Koumbaya/Aegis/pictures/20210312_100416.jpg

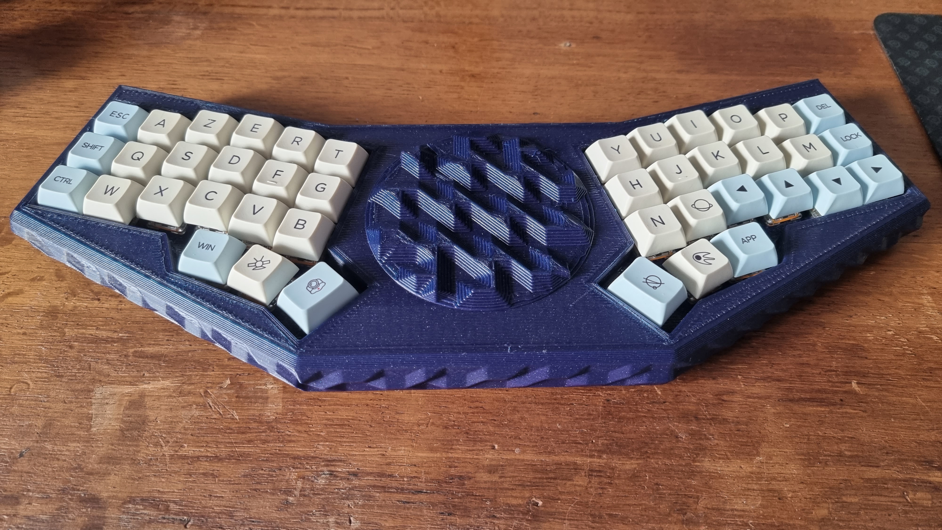
pictures/20210312_100416.jpg
