Koumbaya/Aegis/pictures/20210312_100429.jpg

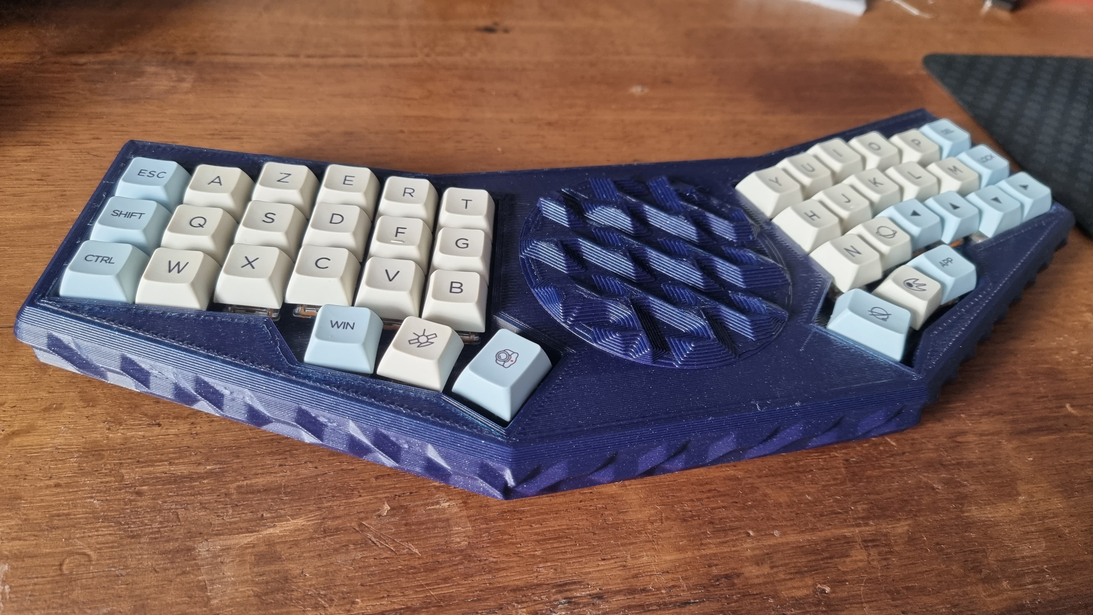
pictures/20210312_100429.jpg
