Koumbaya/Aegis/pictures/20210312_100509.jpg

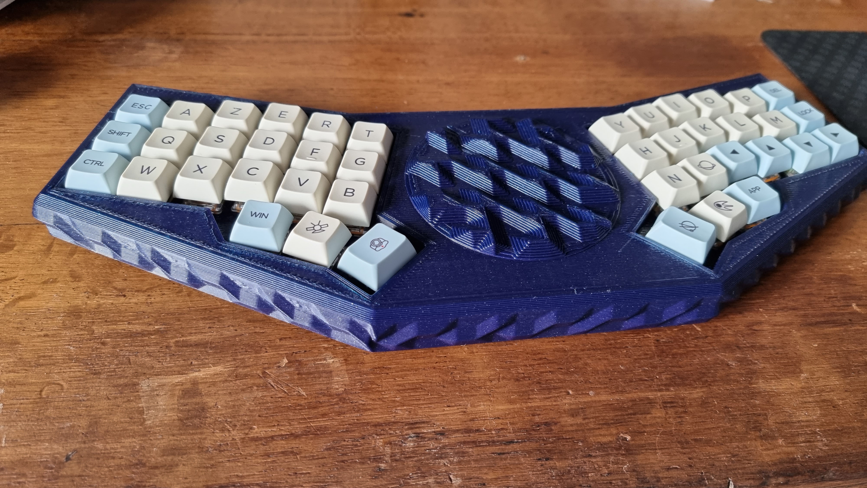
pictures/20210312_100509.jpg
