Koumbaya/Aegis/pictures/20210312_100549.jpg

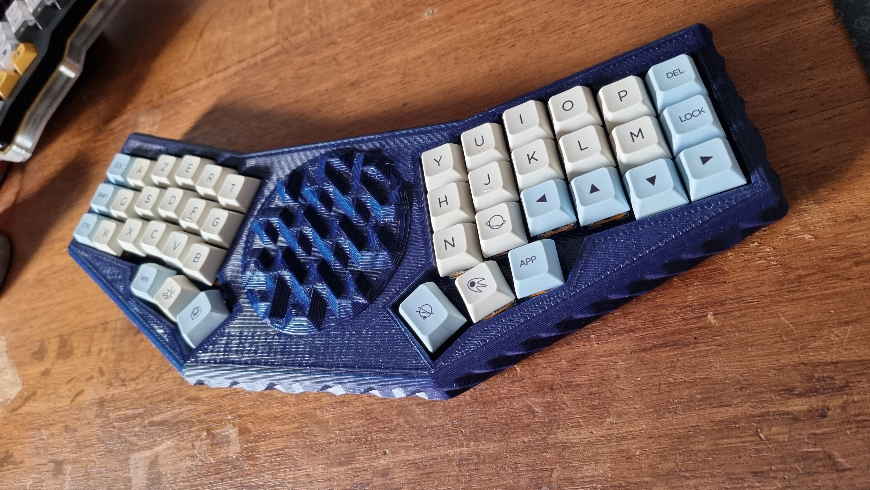
pictures/20210312_100549.jpg
