Koumbaya/Aegis/case_aegis_version/Aegis_bottom.SLDPRT

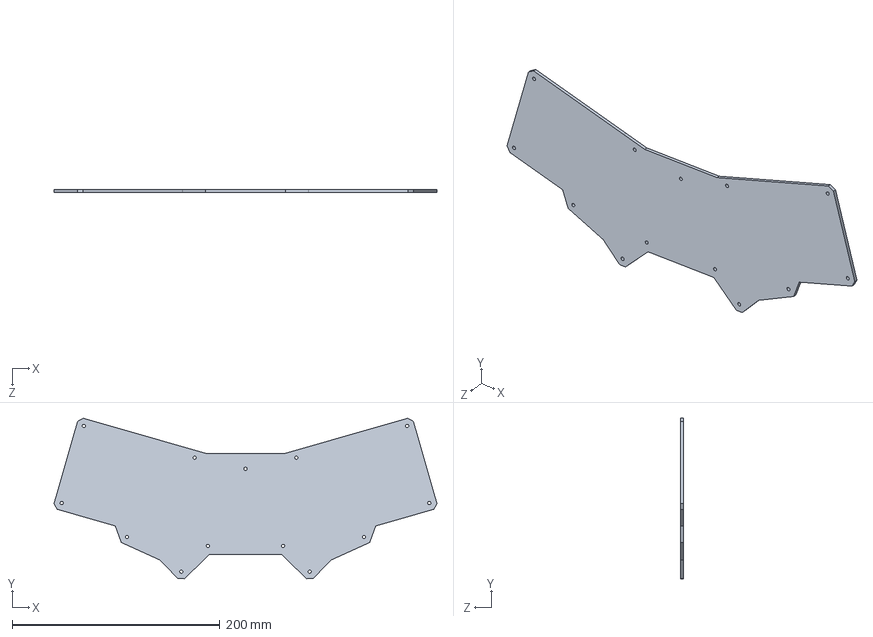
[picture p25: CAD file, 2020-11-01]
case_aegis_version/Aegis_bottom.SLDPRT
369.1 x 154.7 x 3.00 mm
