Koumbaya/Aegis/case_aegis_version/cutouts/Aegis_bottom.DXF

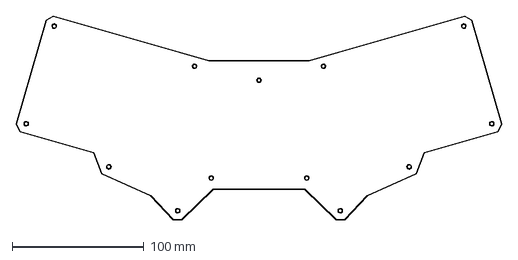
[picture p26: CAD file, 2020-10-25]
case_aegis_version/cutouts/Aegis_bottom.DXF
369.1 x 154.7 mm
