Koumbaya/Aegis/case_crkbd_version/cutouts/Aegis_top2.DXF

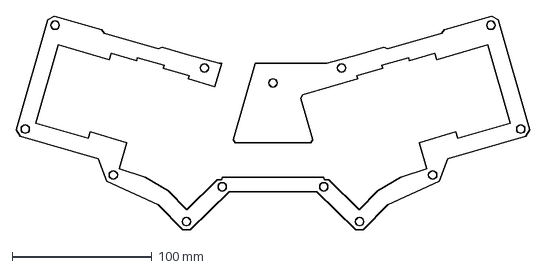
[picture p27: CAD file, 2020-10-31]
case_crkbd_version/cutouts/Aegis_top2.DXF
366.9 x 152.6 mm
