Koumbaya/Aegis/case_aegis_version/Aegis_top1.SLDPRT

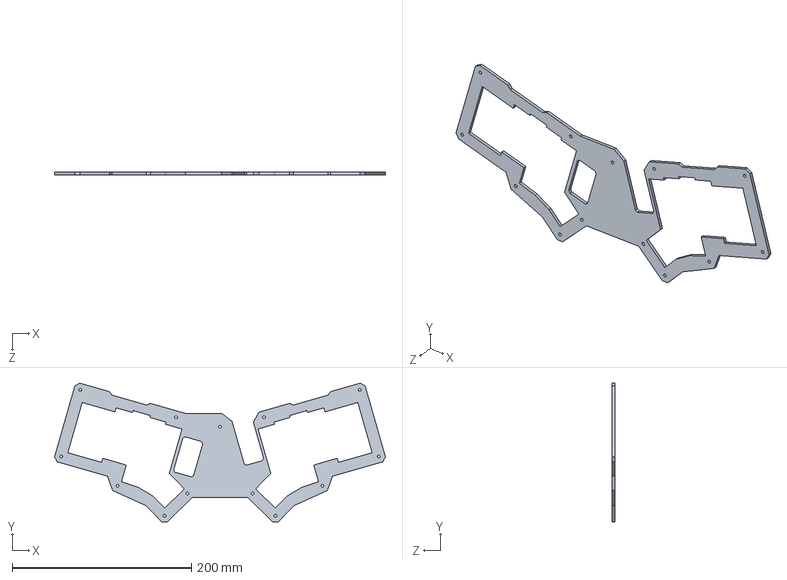
[picture p28: CAD file, 2020-11-01]
case_aegis_version/Aegis_top1.SLDPRT
369.1 x 154.7 x 3.00 mm
