Koumbaya/Aegis/case_aegis_version/cutouts/Aegis_middle.DXF

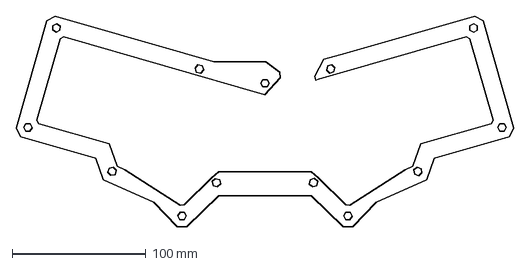
[picture p29: CAD file, 2020-10-25]
case_aegis_version/cutouts/Aegis_middle.DXF
371.9 x 157.4 mm
