Koumbaya/Aegis/case_crkbd_version/Aegis_top2.SLDPRT

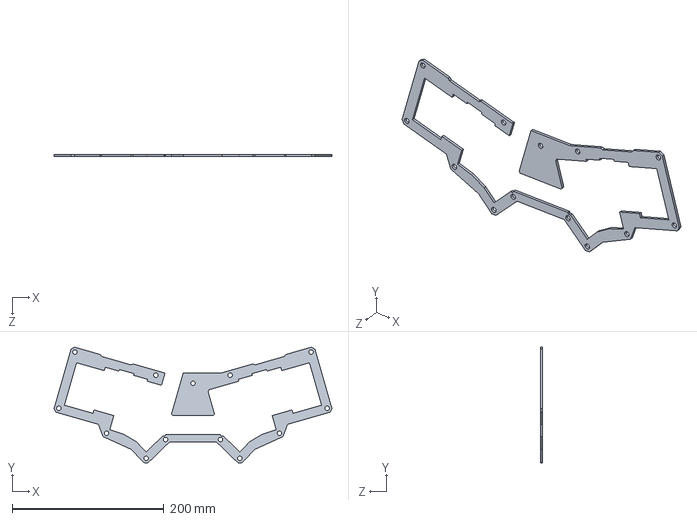
[picture p30: CAD file, 2020-10-31]
case_crkbd_version/Aegis_top2.SLDPRT
366.9 x 152.6 x 3.00 mm
