Koumbaya/Aegis/case_crkbd_version/cutouts/Aegis_top1.DXF

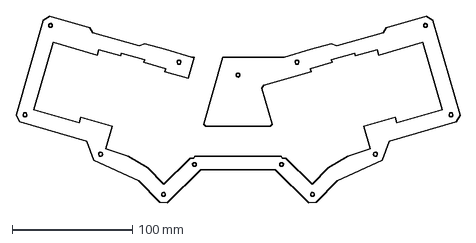
[picture p31: CAD file, 2020-10-31]
case_crkbd_version/cutouts/Aegis_top1.DXF
369.1 x 154.7 mm
