Koumbaya/Aegis/case_aegis_version/Aegis_switch_plate_nologo.SLDPRT

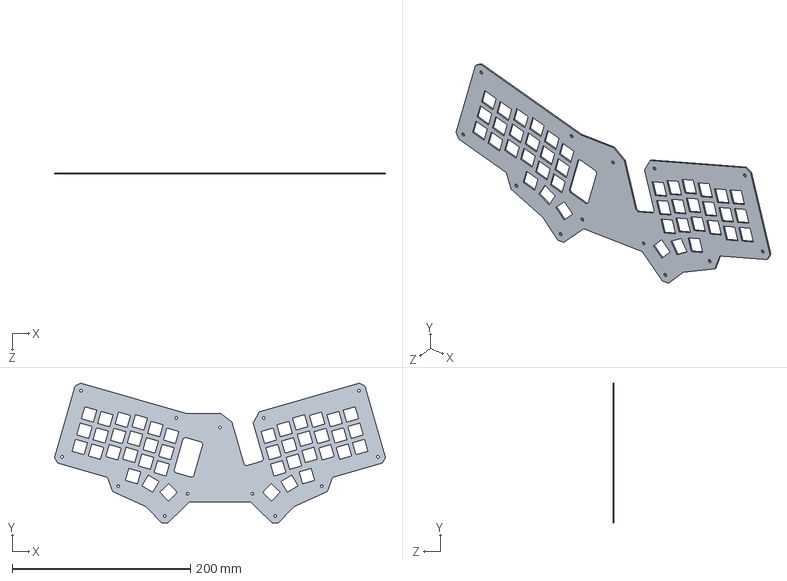
[picture p32: CAD file, 2020-11-01]
case_aegis_version/Aegis_switch_plate_nologo.SLDPRT
371.2 x 156.7 x 1.50 mm
