Koumbaya/Aegis/case_aegis_version/cutouts/Aegis_switch_plate.DXF

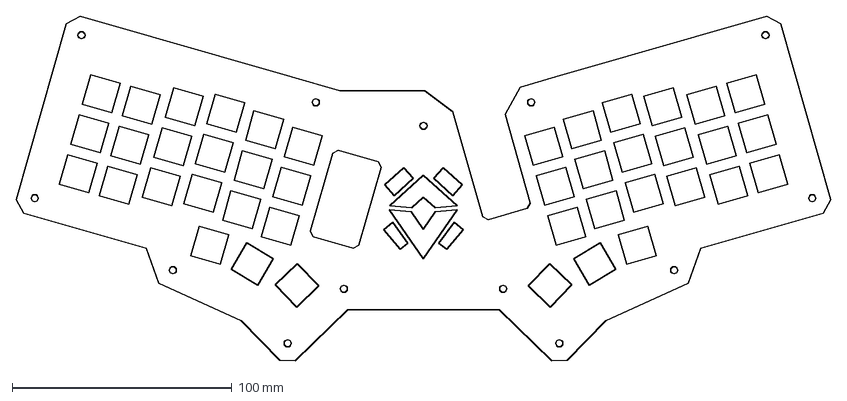
[picture p33: CAD file, 2020-10-25]
case_aegis_version/cutouts/Aegis_switch_plate.DXF
371.2 x 156.7 mm
