Koumbaya/Aegis/case_crkbd_version/Aegis_middle.SLDPRT

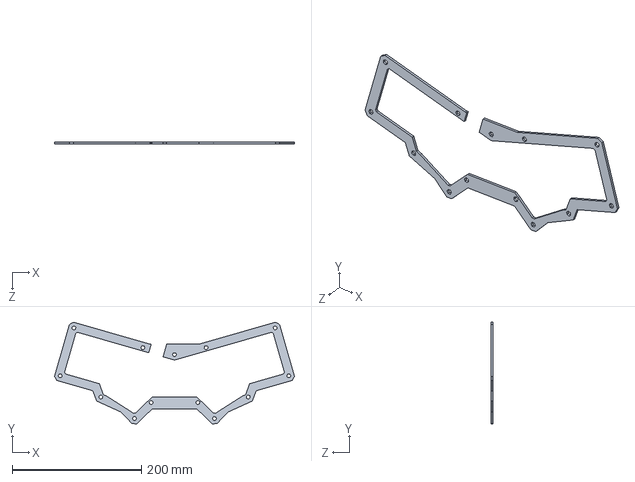
[picture p34: CAD file, 2020-10-31]
case_crkbd_version/Aegis_middle.SLDPRT
371.9 x 157.4 x 3.00 mm
