Koumbaya/Aegis/case_aegis_version/Aegis_top3.SLDPRT

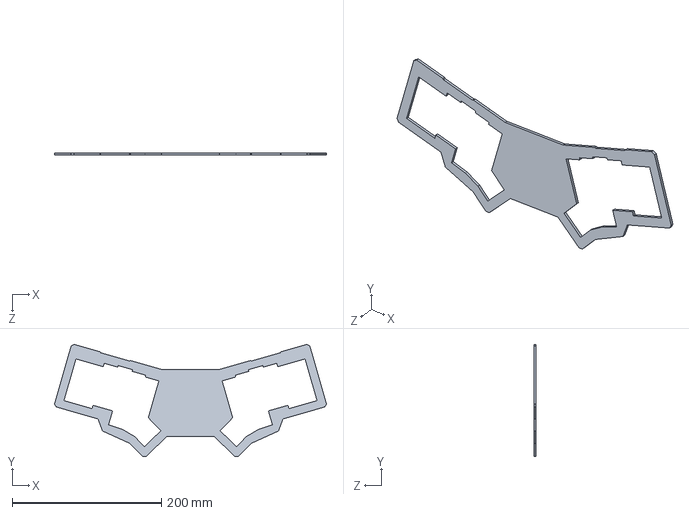
[picture p35: CAD file, 2020-11-01]
case_aegis_version/Aegis_top3.SLDPRT
364.8 x 150.5 x 3.00 mm
