Koumbaya/Aegis/case_aegis_version/cutouts/Aegis_top1.DXF

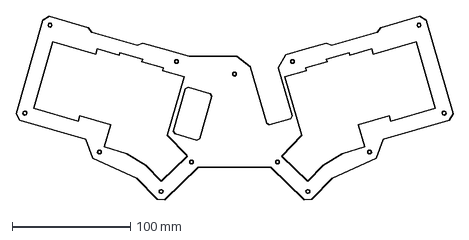
[picture p36: CAD file, 2020-10-25]
case_aegis_version/cutouts/Aegis_top1.DXF
369.1 x 154.7 mm
