Koumbaya/Aegis/case_crkbd_version/cutouts/Aegis_top3.DXF

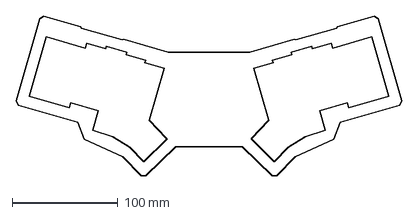
[picture p37: CAD file, 2020-10-25]
case_crkbd_version/cutouts/Aegis_top3.DXF
364.8 x 150.5 mm
