Koumbaya/Aegis/case_crkbd_version/PCB.SLDPRT

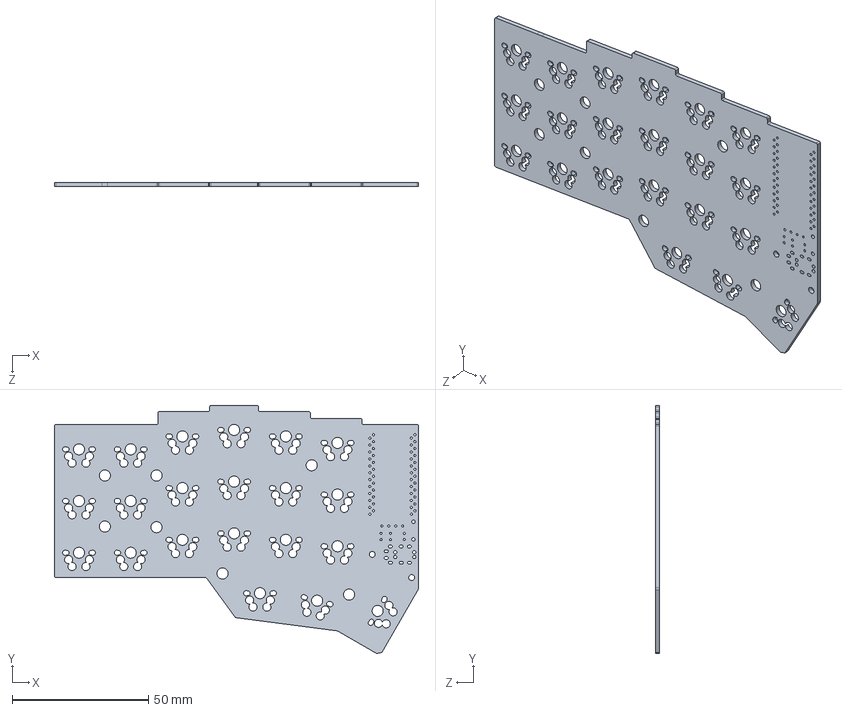
[picture p38: CAD file, 2020-10-31]
case_crkbd_version/PCB.SLDPRT
133.8 x 91.2 x 1.60 mm
