Koumbaya/Aegis/case_aegis_version/Aegis_top2.SLDPRT

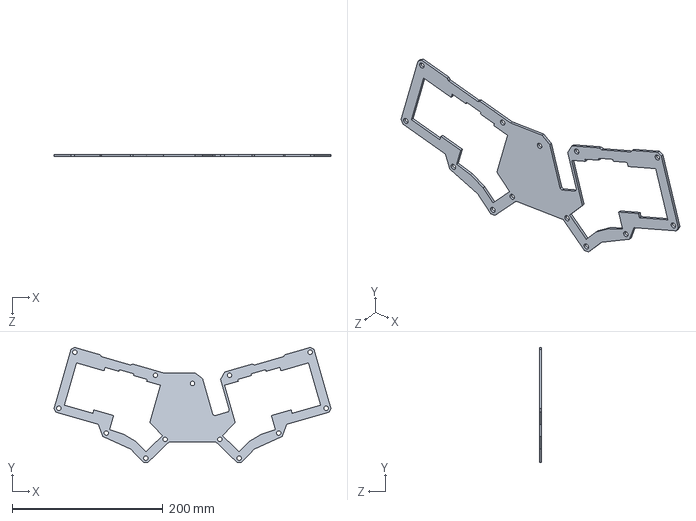
[picture p39: CAD file, 2020-11-01]
case_aegis_version/Aegis_top2.SLDPRT
366.9 x 152.6 x 3.00 mm
