Koumbaya/Aegis/case_aegis_version/cutouts/pcb_model.DXF

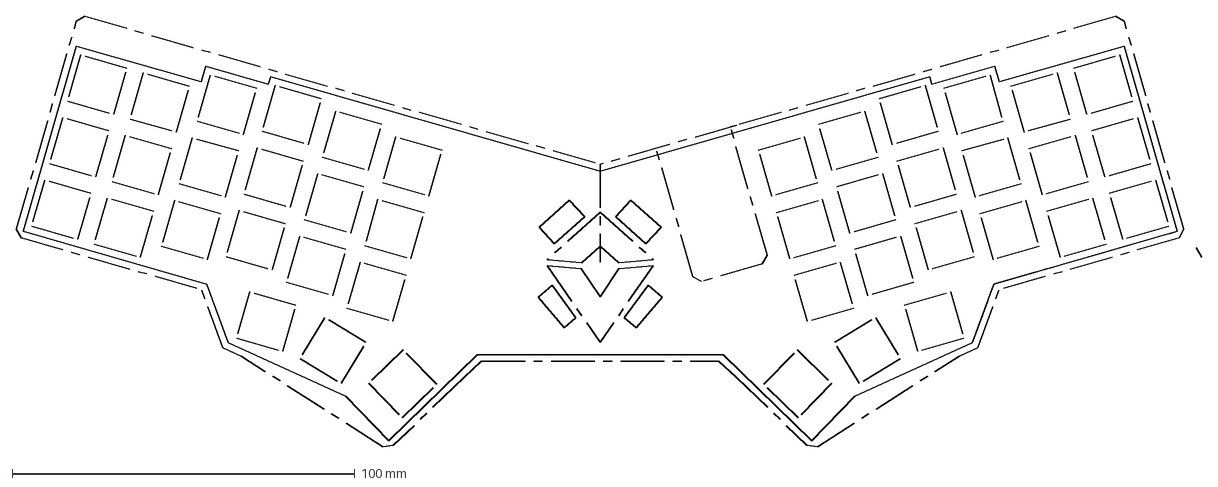
[picture p40: CAD file, 2020-10-24]
case_aegis_version/cutouts/pcb_model.DXF
345.8 x 125.5 mm
