Koumbaya/Aegis/case_aegis_version/Aegis_middle.SLDPRT

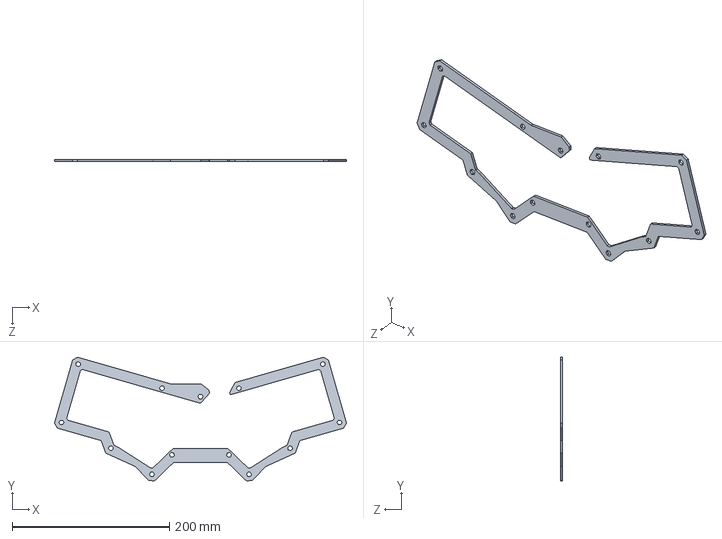
[picture p41: CAD file, 2020-11-01]
case_aegis_version/Aegis_middle.SLDPRT
371.9 x 157.4 x 3.00 mm
