Koumbaya/Aegis/case_aegis_version/Pièce1.SLDPRT

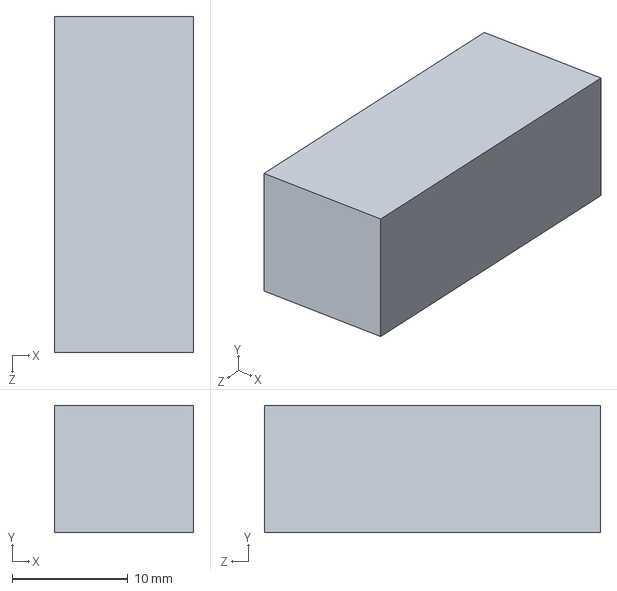
[picture p42: CAD file, 2020-10-24]
case_aegis_version/Pièce1.SLDPRT
12.0 x 11.0 x 29.0 mm
