Koumbaya/Aegis/case_aegis_version/Aegis_switch_plate.SLDPRT

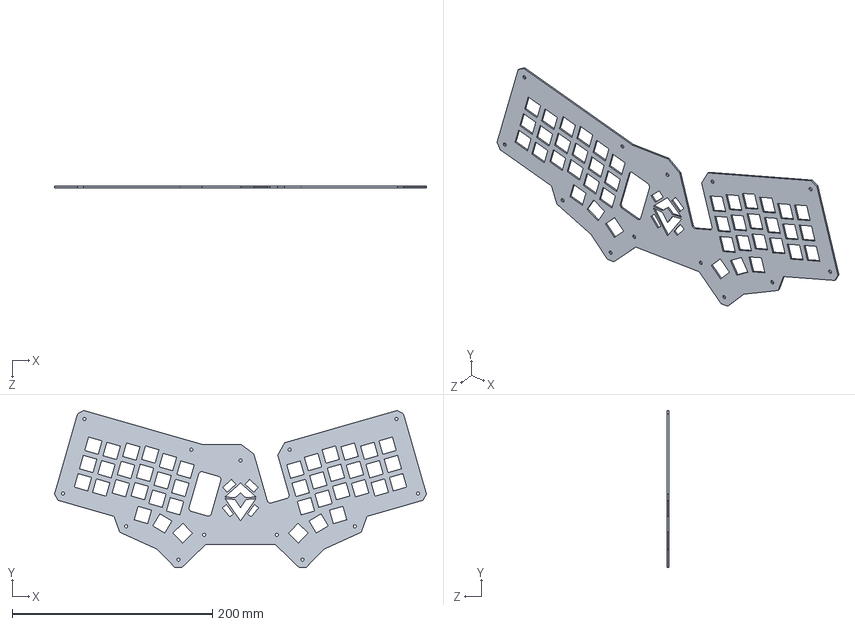
[picture p43: CAD file, 2020-10-24]
case_aegis_version/Aegis_switch_plate.SLDPRT
371.2 x 156.7 x 1.50 mm
