Koumbaya/Aegis/qmk/aegis/aegis.c

#include "aegis.h"

bool process_record_kb(uint16_t keycode, keyrecord_t *record) {
#ifdef SSD1306OLED
  return process_record_gfx(keycode,record) && process_record_user(keycode, record);
#else
  return process_record_user(keycode, record);
#endif
}
